thomai-d/AlarmClock/src/AlarmClock/Icons.cpp

#include "Icons.h"

const byte pgm_edit_data[16][16] PROGMEM = {
	{ 0x0, 0x0, 0x0, 0x0, 0x0, 0x0, 0x0, 0x0, 0x0, 0x0, 0x0, 0x0, 0x33, 0x56, 0x0, 0x0, },
	{ 0x0, 0x0, 0x0, 0x0, 0x0, 0x0, 0x0, 0x0, 0x0, 0x0, 0x0, 0x0, 0xFF, 0xFF, 0xFF, 0x4F, },
	{ 0x0, 0x0, 0x0, 0x0, 0x0, 0x0, 0x0, 0x0, 0x0, 0x0, 0x0, 0x0, 0x0, 0x55, 0xFD, 0xFF, },
	{ 0x0, 0x0, 0x0, 0x0, 0x0, 0x0, 0x0, 0x0, 0x0, 0x0, 0x0, 0xFF, 0xA6, 0x0, 0x0, 0x1E, },
	{ 0x0, 0x0, 0x0, 0x0, 0x0, 0x0, 0x0, 0x0, 0x0, 0x0, 0x6B, 0xFF, 0xFF, 0xFF, 0xC2, 0x0, },
	{ 0x0, 0x0, 0x0, 0x0, 0x0, 0x0, 0x0, 0x0, 0x0, 0x0, 0xFF, 0xFF, 0xFF, 0xFF, 0xBA, 0x0, },
	{ 0x0, 0x0, 0x0, 0x0, 0x0, 0x0, 0x0, 0x0, 0x0, 0x53, 0xFF, 0xAF, 0xFA, 0xFF, 0x10, 0x0, },
	{ 0x0, 0x0, 0x0, 0x0, 0x0, 0x0, 0x0, 0x0, 0x0, 0xF4, 0xFF, 0x0, 0xFF, 0xC8, 0x0, 0x0, },
	{ 0x0, 0x0, 0x0, 0x0, 0x0, 0x0, 0x0, 0x0, 0x3B, 0xFF, 0x7B, 0x92, 0xFF, 0x26, 0x0, 0x0, },
	{ 0x0, 0x0, 0x0, 0x0, 0x0, 0x0, 0x0, 0x0, 0xDD, 0xFF, 0x0, 0xFF, 0xE0, 0x0, 0x0, 0x0, },
	{ 0x0, 0x0, 0x0, 0x0, 0x0, 0x0, 0x0, 0x35, 0xFF, 0x95, 0x78, 0xFF, 0x3E, 0x0, 0x0, 0x0, },
	{ 0x0, 0x0, 0x0, 0x0, 0x0, 0x0, 0x0, 0x0, 0x9A, 0x10, 0xFF, 0xF8, 0x0, 0x0, 0x0, 0x0, },
	{ 0x0, 0x0, 0x0, 0x0, 0x0, 0x0, 0x0, 0x54, 0x0, 0x0, 0x80, 0x52, 0x0, 0x0, 0x0, 0x0, },
	{ 0x10, 0x10, 0x10, 0x10, 0x11, 0x11, 0x0, 0xFF, 0xFF, 0xA1, 0x0, 0x0, 0x0, 0x0, 0x0, 0x0, },
	{ 0xFF, 0xFF, 0xFF, 0xFF, 0xFF, 0xFF, 0x0, 0xC5, 0xFF, 0xD8, 0x0, 0x0, 0x0, 0x0, 0x0, 0x0, },
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
{
	for (int y = 0; y < 16; y++)
	{
		for (int x = 0; x < 16; x++)
		{
			uint16_t c = pgm_read_byte_near(&(data[y][x]));
			Display.setColor(c * r / 256, c * g / 256, c * b / 256);
			Display.drawPixel(xpos + x, ypos + y);
		}
	}
}
